ayushmanyadav2006/Flight-Controller-/Flight Controller Routing.png

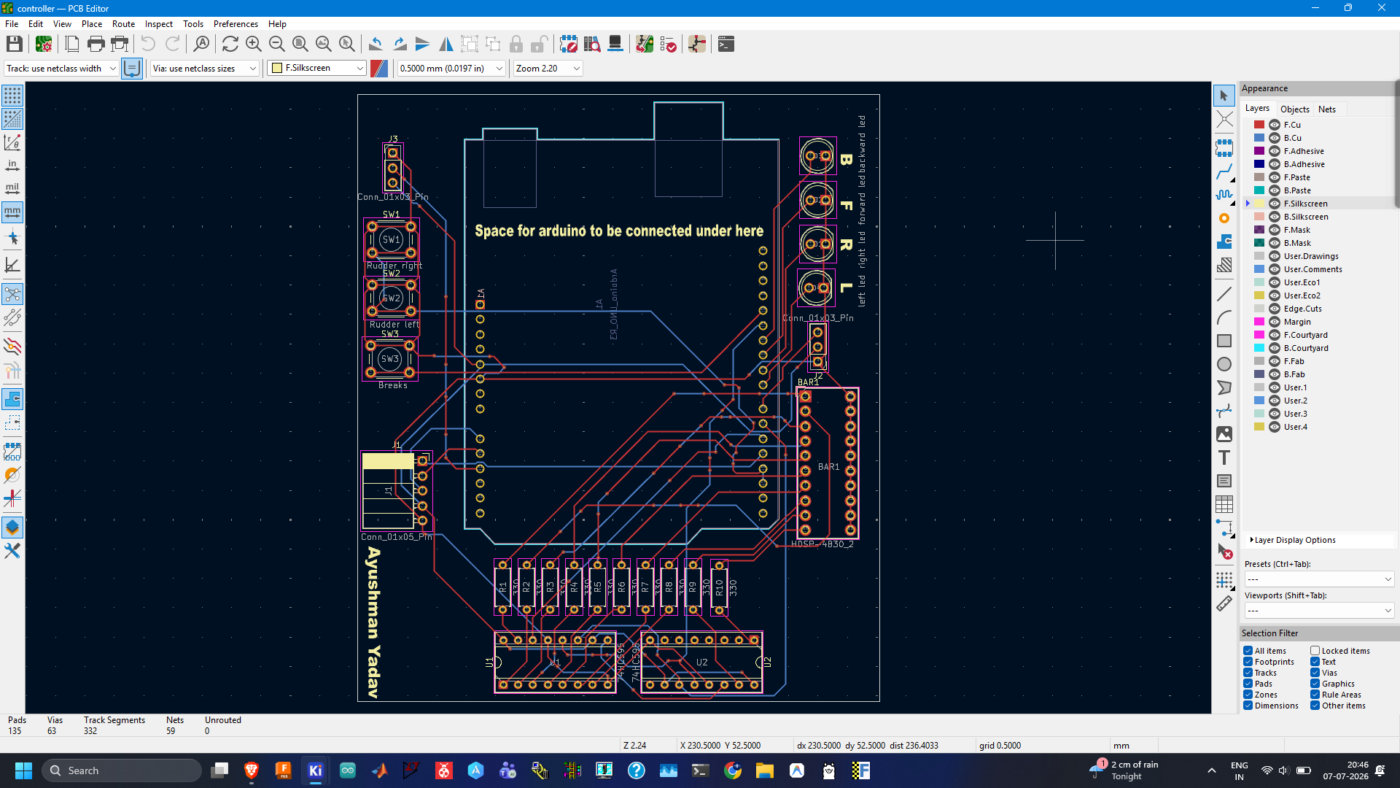
Flight Controller Routing.png
