ayushmanyadav2006/Flight-Controller-/Servo to Arduino.png

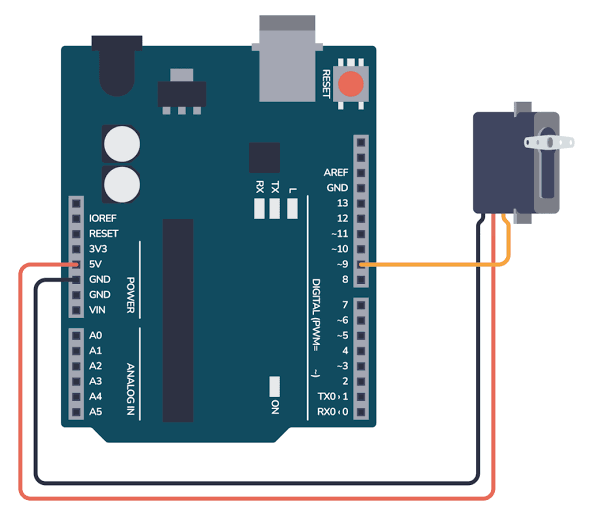
Servo to Arduino.png
